riacob/ESP32_AirStick/Firmware/ESP32_AirStick/include/mqtt_cfg.h

#ifndef _MQTT_CFG_H
#define _MQTT_CFG_H

//#define TOPIC_DISCOVERY_TEMPERATURE "homeassistant/sensor/esp32_temperature/config"
//#define TOPIC_DISCOVERY_HUMIDITY "homeassistant/sensor/esp32_humidity/config"
//#define PAYLOAD_DISCOVERY_TEMPERATURE "{\"name\":\"ESP32 Temperature\",\"state_topic\":\"homeassistant/sensor/esp32_temperature/state\",\"unit_of_measurement\":\"°C\",\"device_class\": \"temperature\"}"
//#define PAYLOAD_DISCOVERY_HUMIDITY "{\"name\":\"ESP32 Humidity\",\"state_topic\":\"homeassistant/sensor/esp32_humidity/state\",\"unit_of_measurement\":\"%\",\"device_class\": \"humidity\"}"
//#define TOPIC_TEMPERATURE "homeassistant/sensor/esp32_temperature/state"
//#define TOPIC_HUMIDITY "homeassistant/sensor/esp32_humidity/state"


#endif
